ZhikaiZhang1/PUMA_REPO/Mechanical/Motor Clamp 8 Top.STL

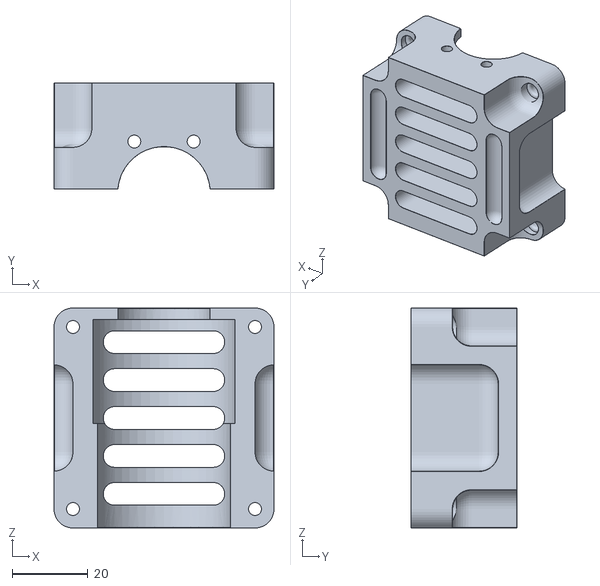
[picture p9: CAD file, 2020-07-20]
Mechanical/Motor Clamp 8 Top.STL
58.0 x 28.0 x 58.0
