ZhikaiZhang1/PUMA_REPO/Mechanical/Motor Mounting Bracket Bottom.STL

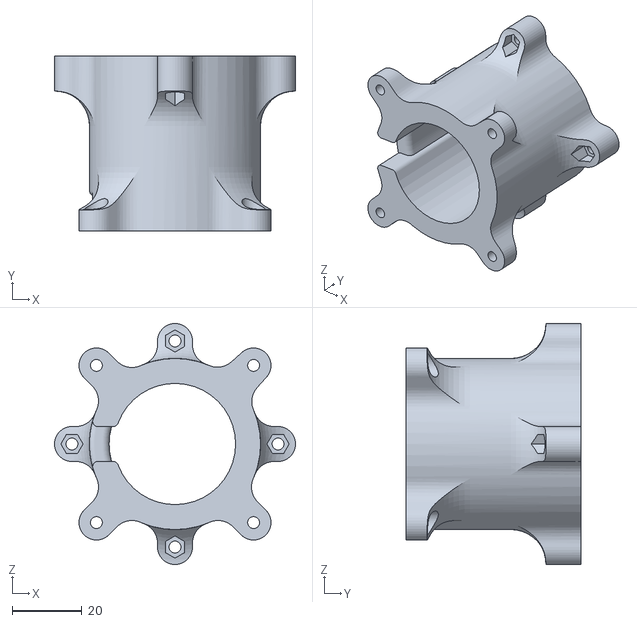
[picture p10: CAD file, 2020-07-14]
Mechanical/Motor Mounting Bracket Bottom.STL
69.0 x 50.0 x 69.0
