ZhikaiZhang1/PUMA_REPO/Mechanical/Motor Mounting Bracket Top.STL

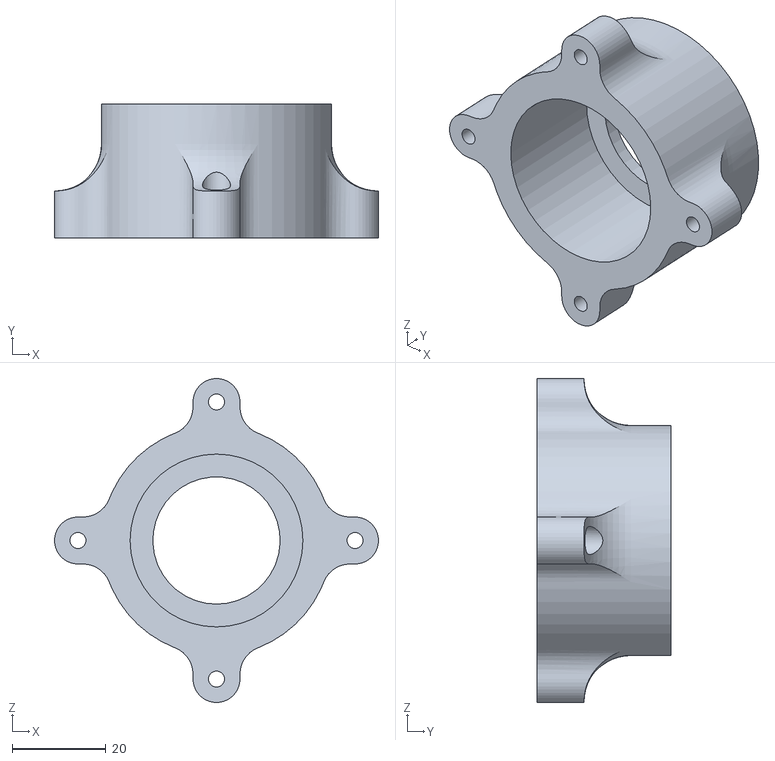
[picture p11: CAD file, 2020-07-14]
Mechanical/Motor Mounting Bracket Top.STL
69.0 x 28.5 x 69.0
