ZhikaiZhang1/PUMA_REPO/Mechanical/Arm 4.02.STL

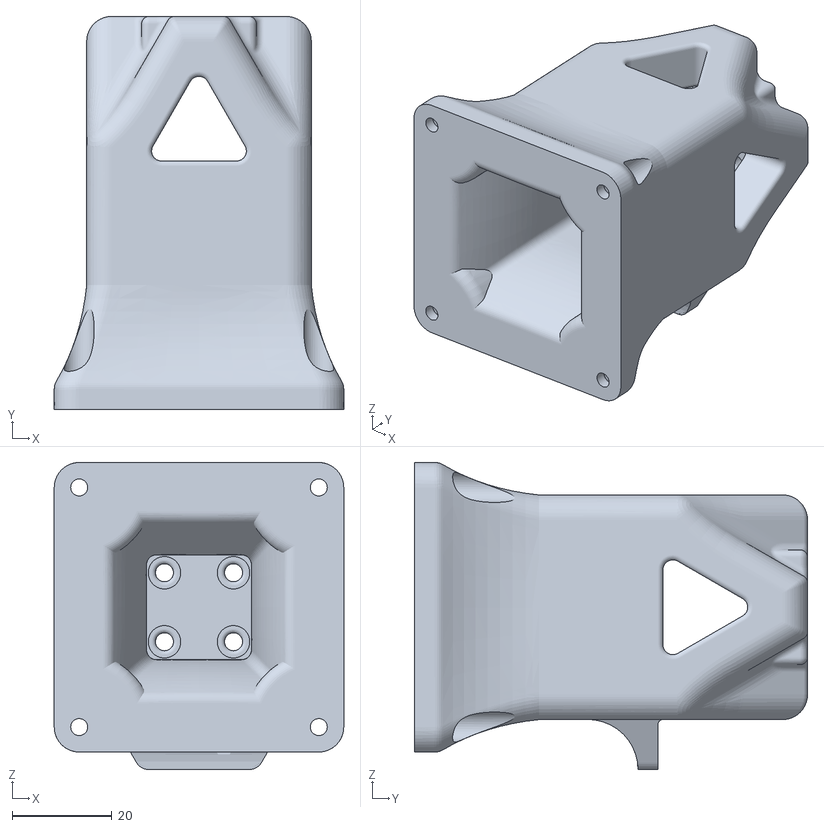
[picture p12: CAD file, 2020-07-10]
Mechanical/Arm 4.02.STL
58.0 x 78.8 x 61.5
