ZhikaiZhang1/PUMA_REPO/Mechanical/Arm 4.STL

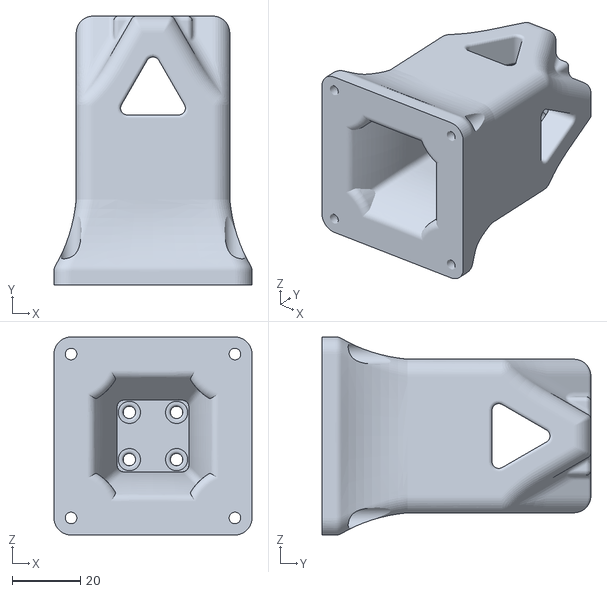
[picture p13: CAD file, 2020-07-07]
Mechanical/Arm 4.STL
58.0 x 78.8 x 58.0
