ZhikaiZhang1/PUMA_REPO/Mechanical/Link 7.5-180.STL

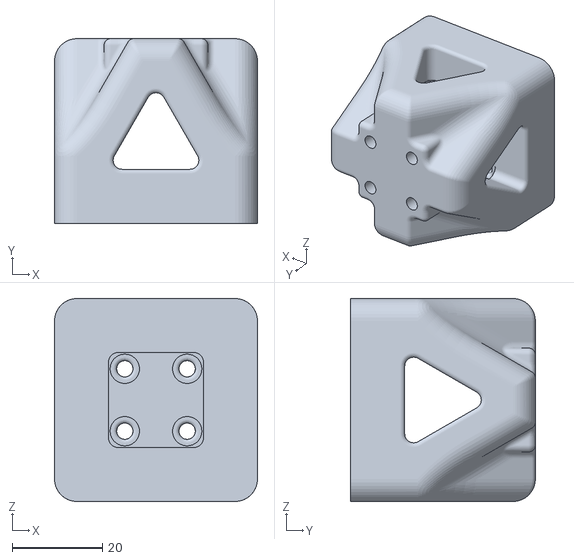
[picture p14: CAD file, 2020-07-04]
Mechanical/Link 7.5-180.STL
45.0 x 41.0 x 45.0
