ZhikaiZhang1/PUMA_REPO/Mechanical/Link 7.5-90.STL

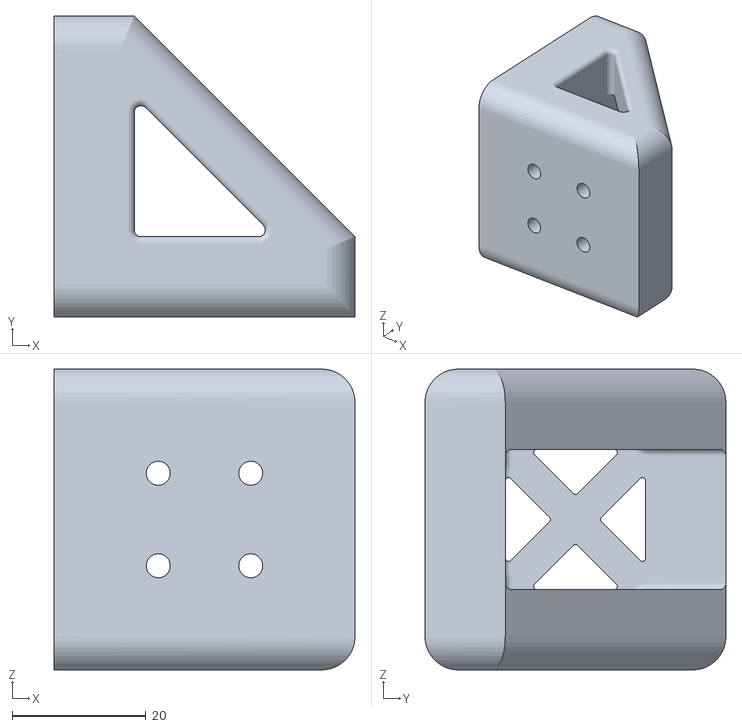
[picture p15: CAD file, 2020-07-04]
Mechanical/Link 7.5-90.STL
45.0 x 45.0 x 45.0
