ZhikaiZhang1/PUMA_REPO/Mechanical/Motor Clamp 7.5 Bottom.STL

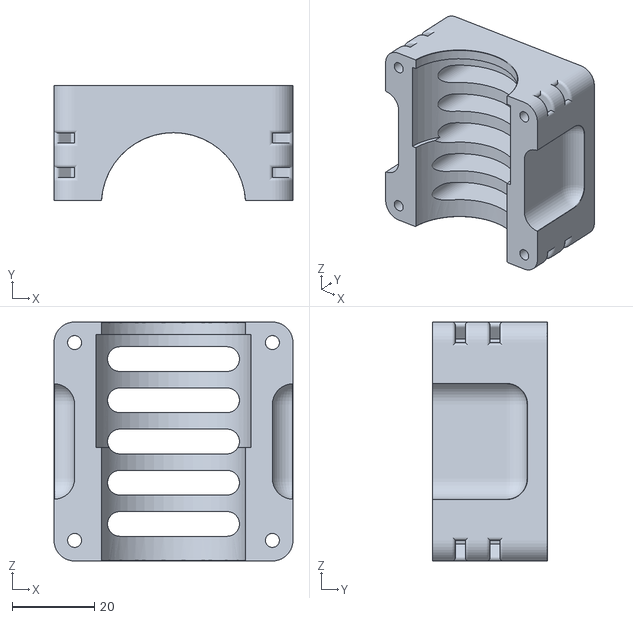
[picture p16: CAD file, 2020-07-02]
Mechanical/Motor Clamp 7.5 Bottom.STL
58.0 x 28.0 x 58.0
