ZhikaiZhang1/PUMA_REPO/Mechanical/Link 7.5.STL

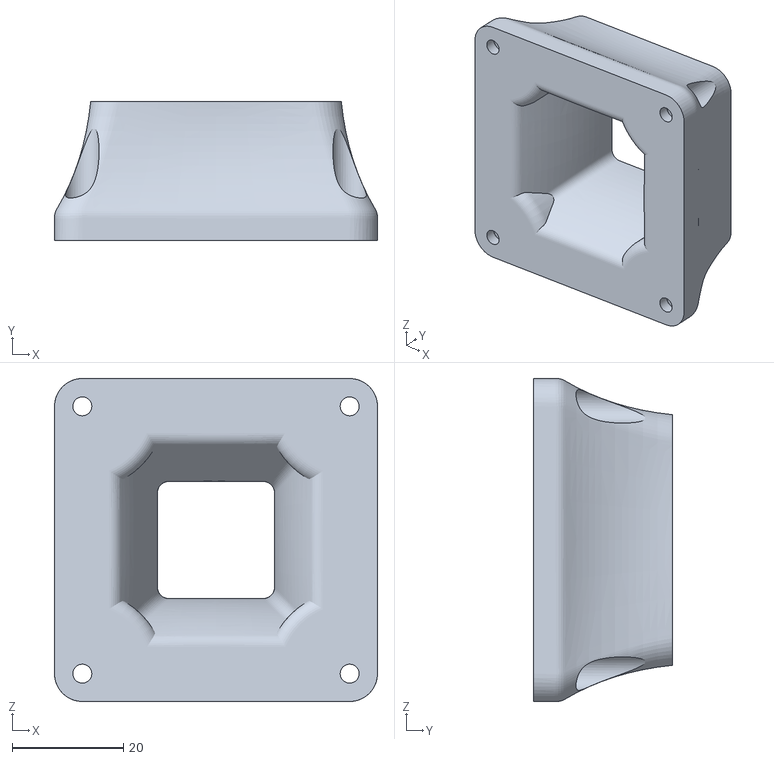
[picture p17: CAD file, 2020-07-02]
Mechanical/Link 7.5.STL
58.0 x 25.0 x 58.0
