ZhikaiZhang1/PUMA_REPO/Mechanical/Link 5.STL

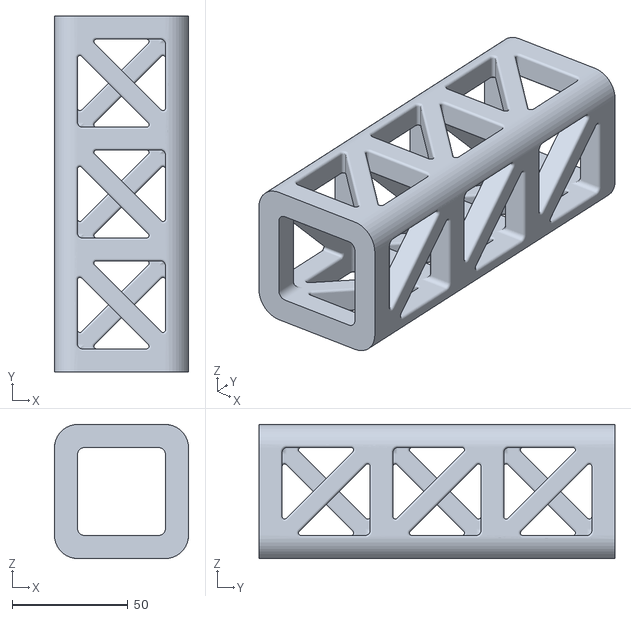
[picture p18: CAD file, 2020-06-23]
Mechanical/Link 5.STL
58.0 x 154.0 x 58.0
