ZhikaiZhang1/PUMA_REPO/Mechanical/Link 4.STL

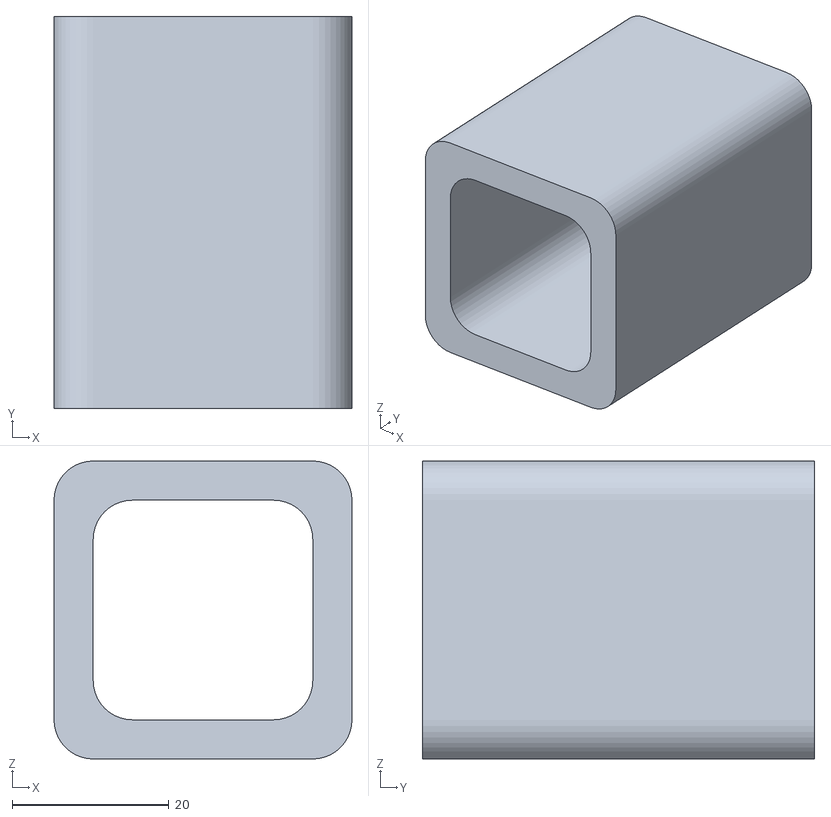
[picture p19: CAD file, 2020-06-16]
Mechanical/Link 4.STL
38.0 x 50.0 x 38.0
