ZhikaiZhang1/PUMA_REPO/Mechanical/Link 3.STL

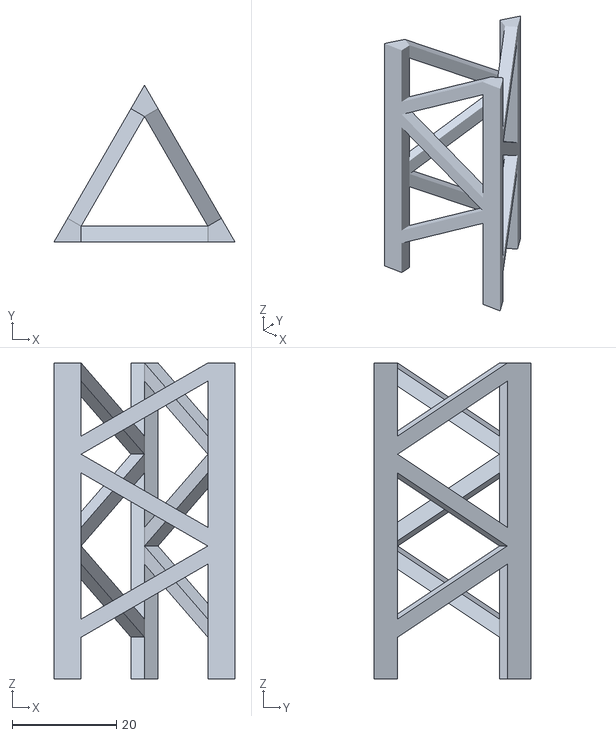
[picture p20: CAD file, 2020-06-16]
Mechanical/Link 3.STL
34.6 x 30.0 x 60.5
