ZhikaiZhang1/PUMA_REPO/Mechanical/Motor Shaft Coupler Test 1.STL

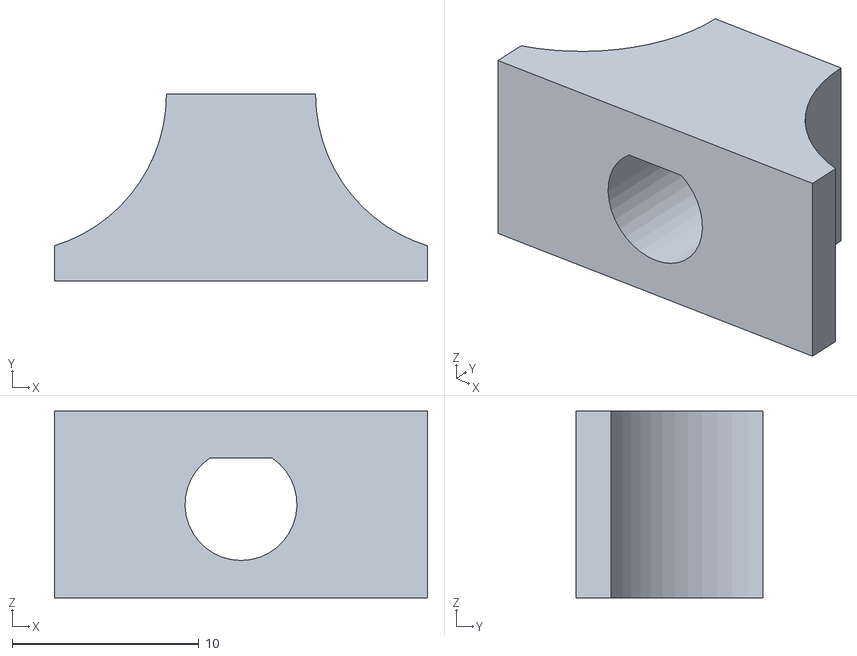
[picture p21: CAD file, 2020-06-04]
Mechanical/Motor Shaft Coupler Test 1.STL
20.0 x 10.0 x 10.0
