ZhikaiZhang1/PUMA_REPO/Mechanical/Clamp Test Top 3.STL

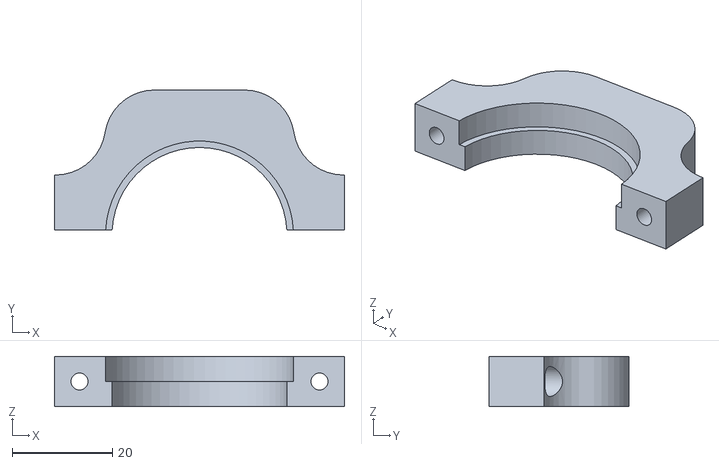
[picture p23: CAD file, 2020-06-03]
Mechanical/Clamp Test Top 3.STL
58.0 x 28.0 x 10.0
