ZhikaiZhang1/PUMA_REPO/Mechanical/Link 2.STL

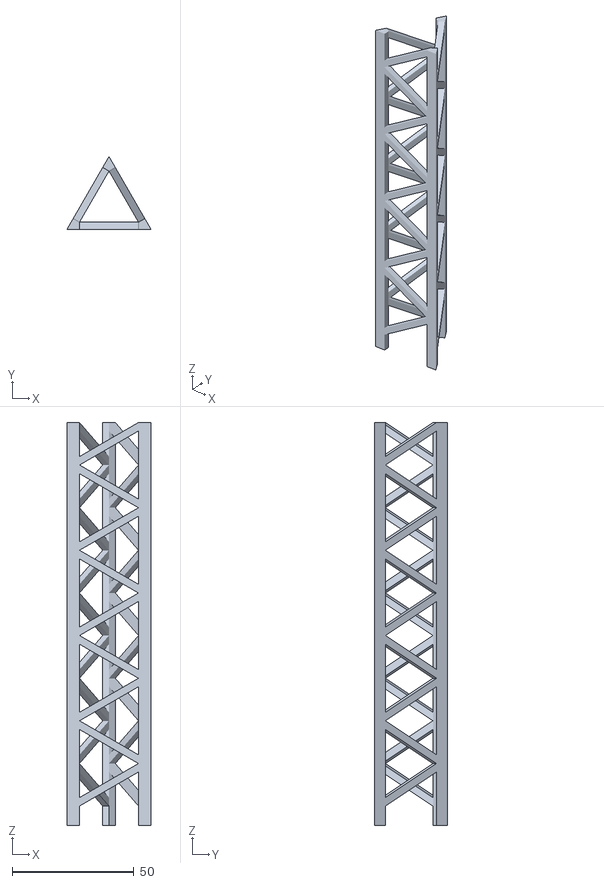
[picture p24: CAD file, 2020-05-25]
Mechanical/Link 2.STL
34.6 x 30.0 x 165.6
