ZhikaiZhang1/PUMA_REPO/Mechanical/Hardware Test 3 Bottom.STL

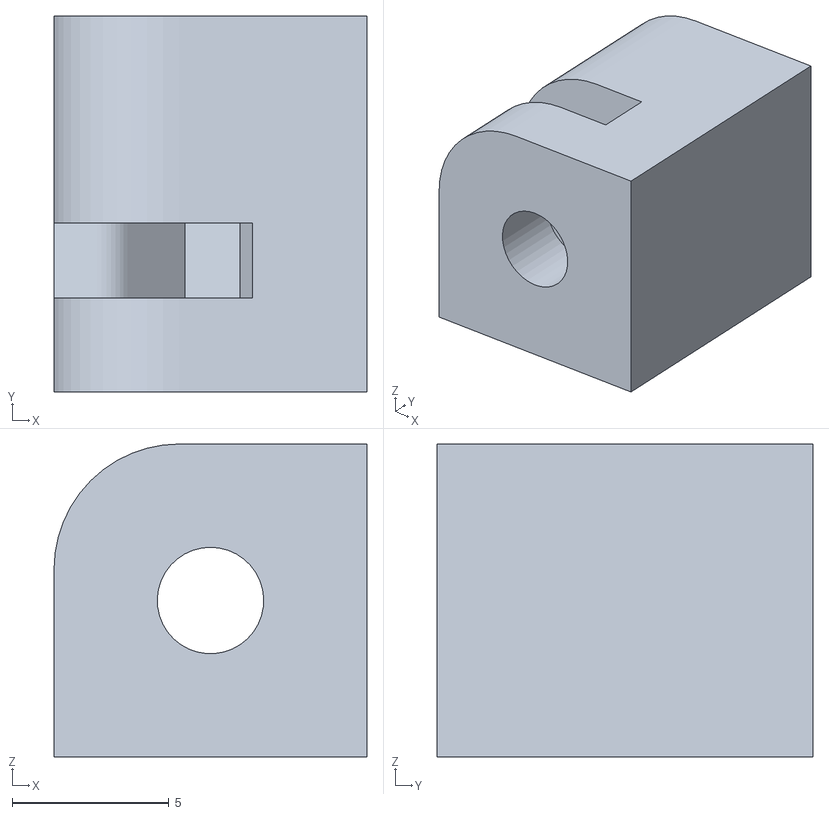
[picture p25: CAD file, 2020-05-25]
Mechanical/Hardware Test 3 Bottom.STL
10.0 x 12.0 x 10.0
