ZhikaiZhang1/PUMA_REPO/Mechanical/Hardware Test 2 Bottom.STL

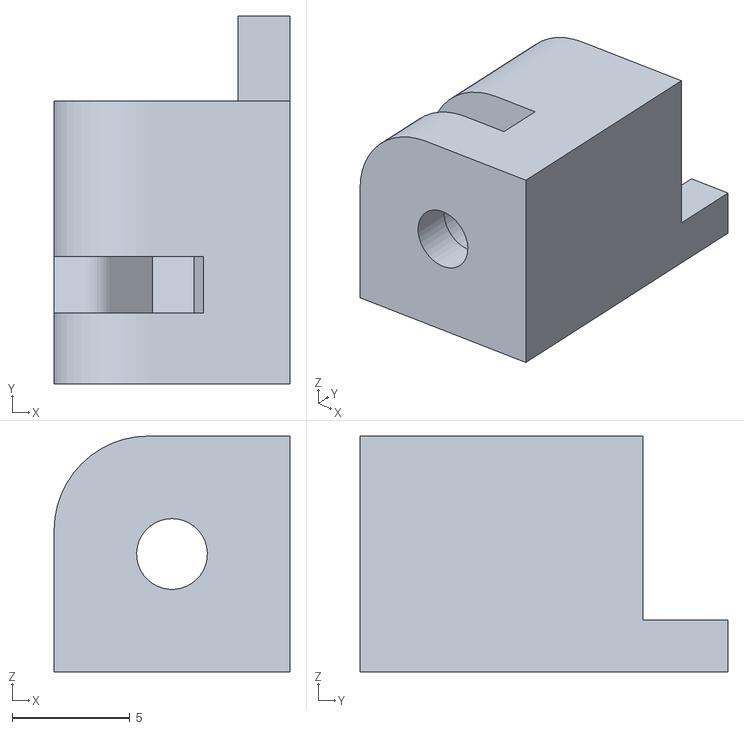
[picture p27: CAD file, 2020-05-25]
Mechanical/Hardware Test 2 Bottom.STL
10.0 x 15.6 x 10.0
