ZhikaiZhang1/PUMA_REPO/Mechanical/Hardware Test 1 Top.STL

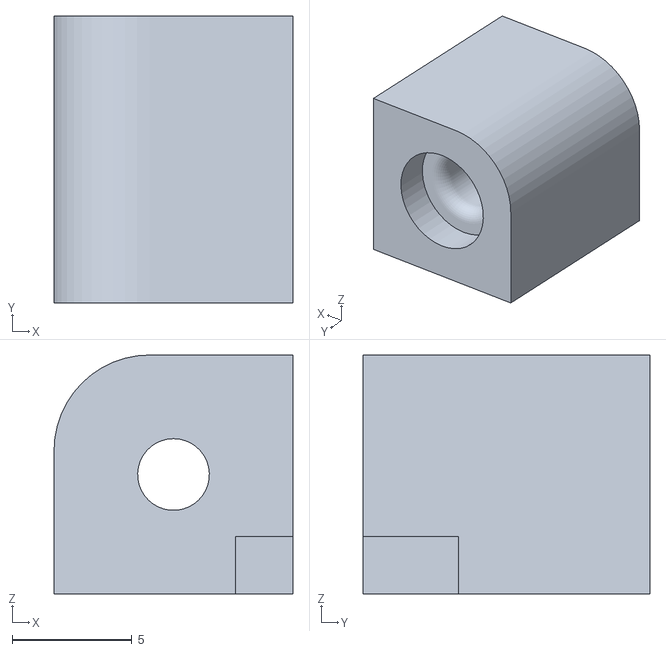
[picture p28: CAD file, 2020-05-25]
Mechanical/Hardware Test 1 Top.STL
10.0 x 12.0 x 10.0
