ZhikaiZhang1/PUMA_REPO/Mechanical/Hardware Test 1 Bottom.STL

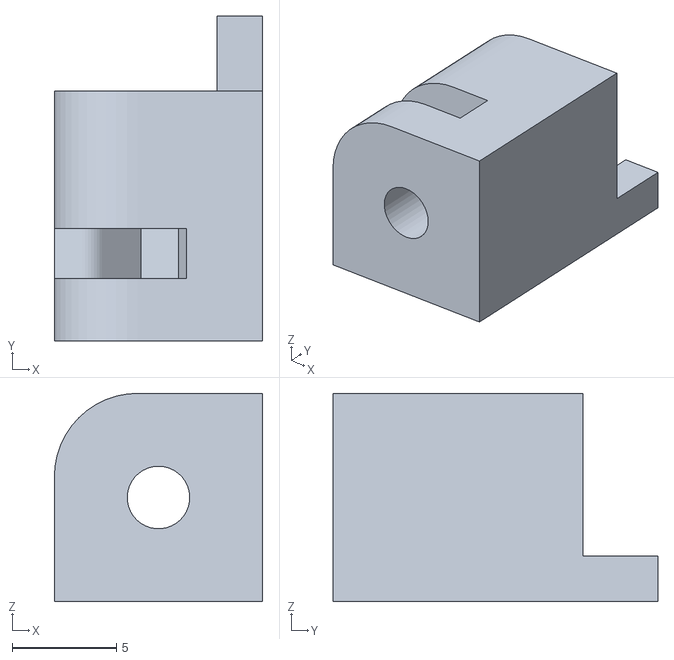
[picture p29: CAD file, 2020-05-25]
Mechanical/Hardware Test 1 Bottom.STL
10.0 x 15.6 x 10.0
