ZhikaiZhang1/PUMA_REPO/Mechanical/Square Test Male.SLDPRT

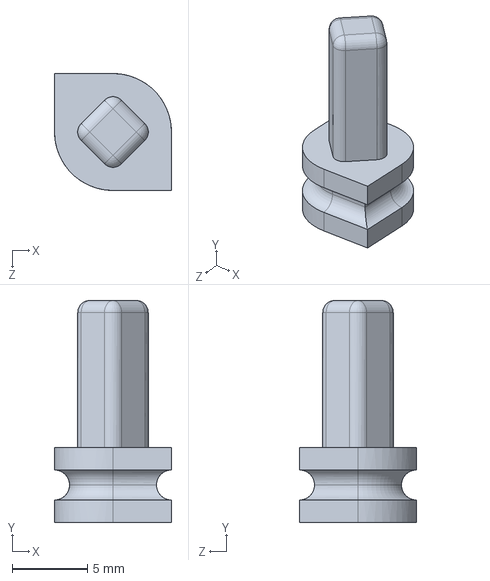
[picture p30: CAD file, 2020-05-19]
Mechanical/Square Test Male.SLDPRT
7.80 x 14.8 x 7.80 mm
