ZhikaiZhang1/PUMA_REPO/Mechanical/Round Test Male.SLDPRT

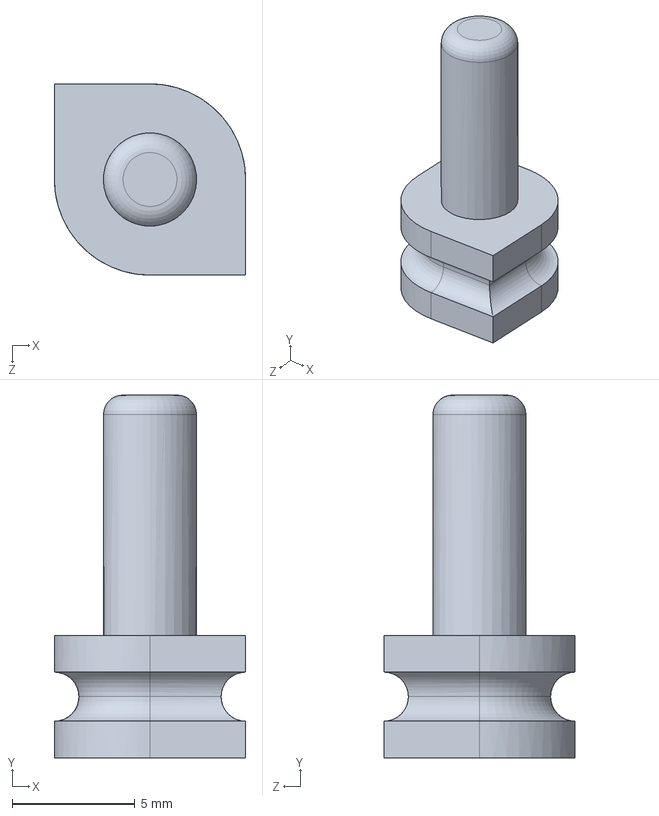
[picture p31: CAD file, 2020-05-19]
Mechanical/Round Test Male.SLDPRT
7.80 x 14.8 x 7.80 mm
