ZhikaiZhang1/PUMA_REPO/Mechanical/Square Test Female.SLDPRT

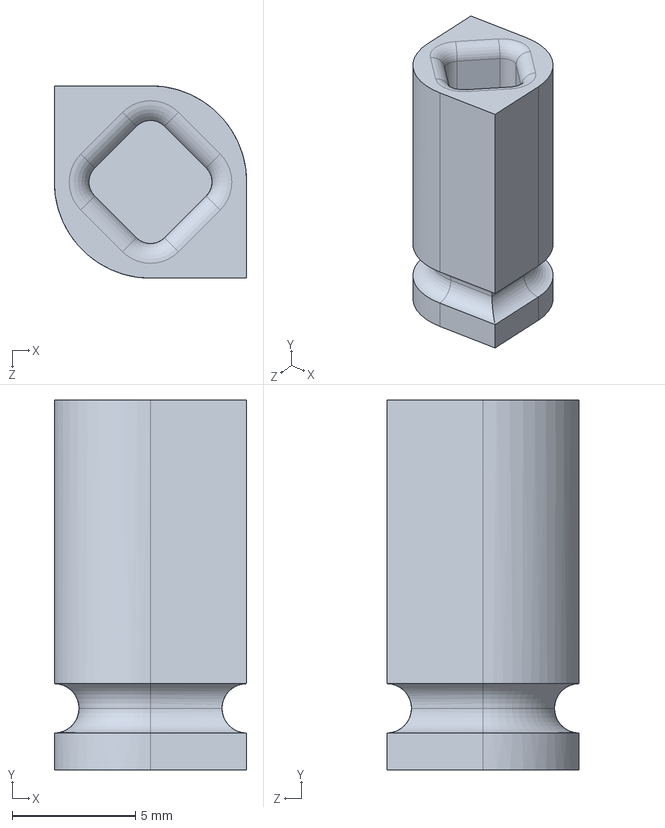
[picture p32: CAD file, 2020-05-19]
Mechanical/Square Test Female.SLDPRT
7.80 x 15.0 x 7.80 mm
