ZhikaiZhang1/PUMA_REPO/Mechanical/Round Test Female 5.SLDPRT

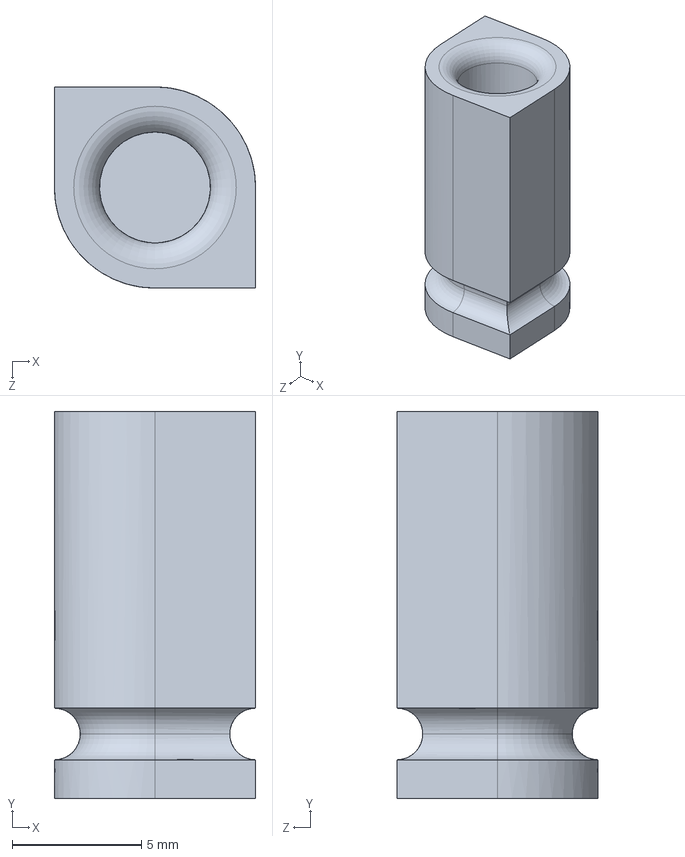
[picture p33: CAD file, 2020-05-19]
Mechanical/Round Test Female 5.SLDPRT
7.80 x 15.0 x 7.80 mm
